Ankwyell/Prusa3/reprap-i3/doc/framestep1.png

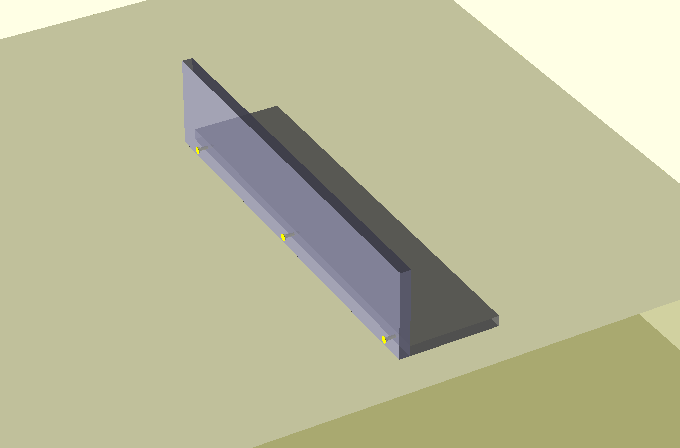
reprap-i3/doc/framestep1.png
