Ankwyell/Prusa3/reprap-i3/doc/framestep3.png

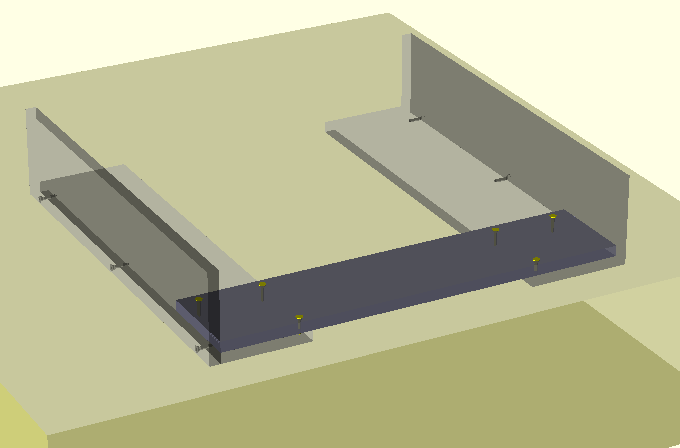
reprap-i3/doc/framestep3.png
