Ankwyell/Prusa3/reprap-i3/doc/framestep5.png

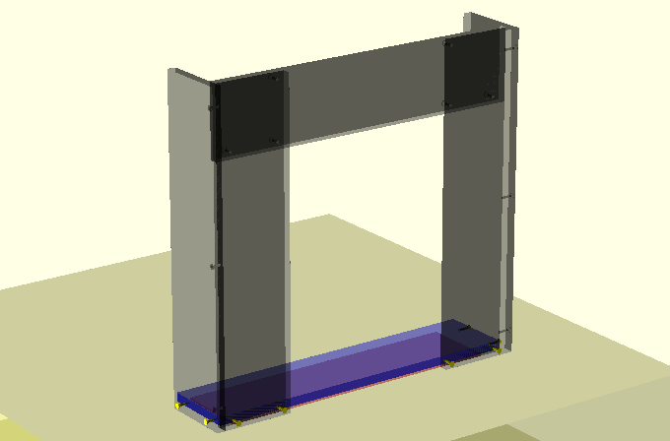
reprap-i3/doc/framestep5.png
