Ankwyell/Prusa3/reprap-i3/doc/ystep1.png

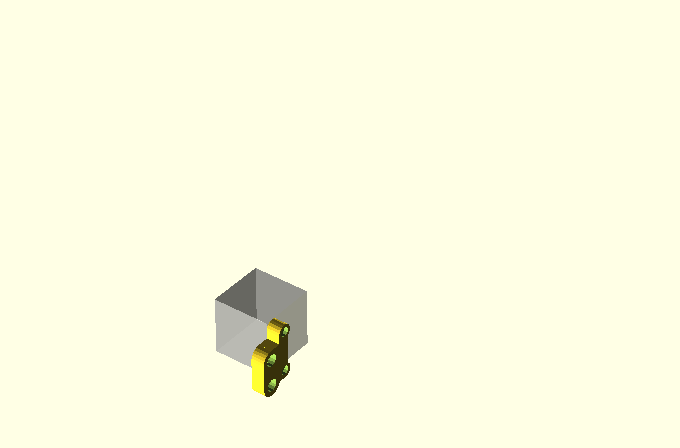
reprap-i3/doc/ystep1.png
