Ankwyell/Prusa3/reprap-i3/doc/ystep3.png

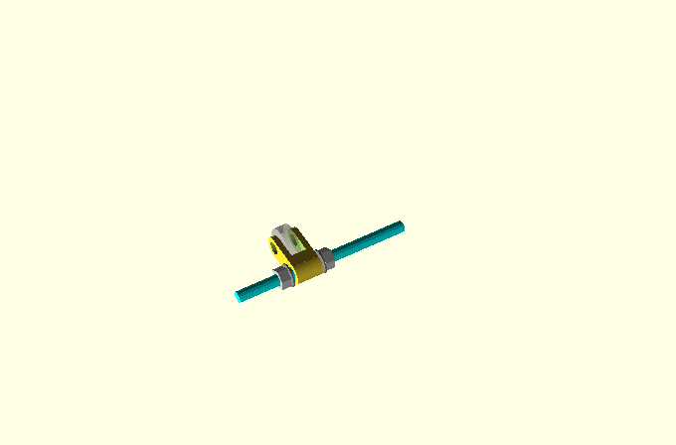
reprap-i3/doc/ystep3.png
