Ankwyell/Prusa3/reprap-i3/doc/ystep6.png

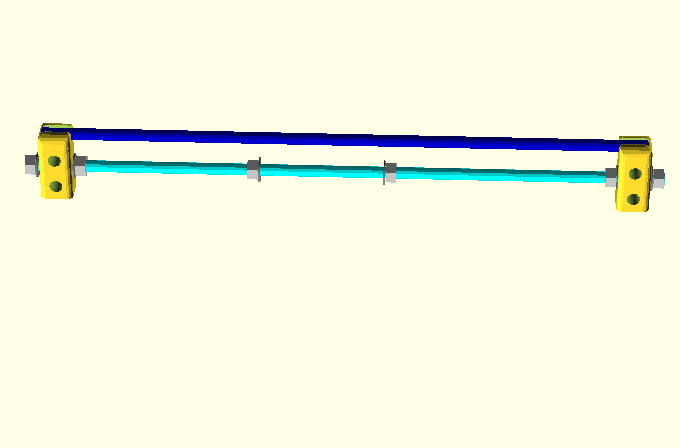
reprap-i3/doc/ystep6.png
