Ankwyell/Prusa3/reprap-i3/doc/ystep7.png

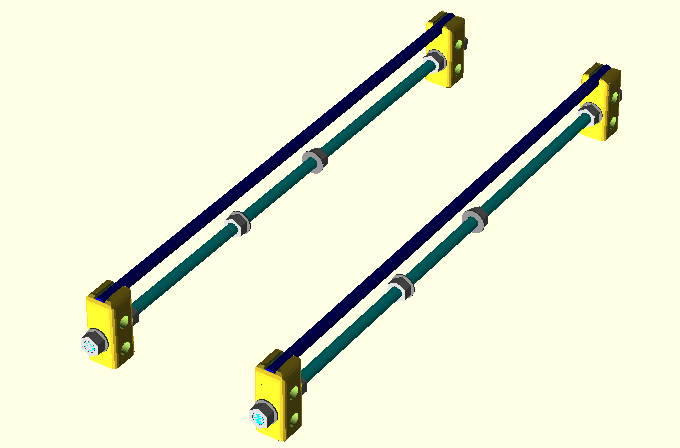
reprap-i3/doc/ystep7.png
