Ankwyell/Prusa3/reprap-i3/doc/ystep8.png

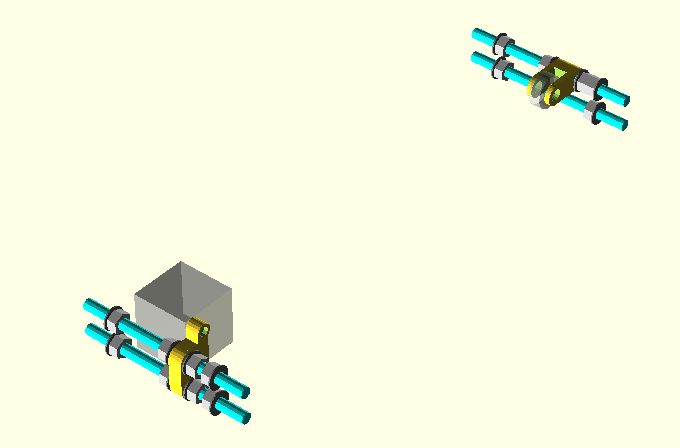
reprap-i3/doc/ystep8.png
