Ankwyell/Prusa3/reprap-i3/doc/ystep9.png

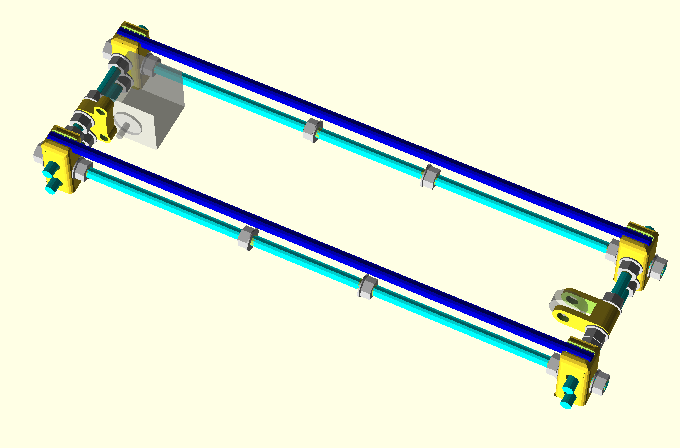
reprap-i3/doc/ystep9.png
