Ankwyell/Prusa3/reprap-i3/doc/ystep10.png

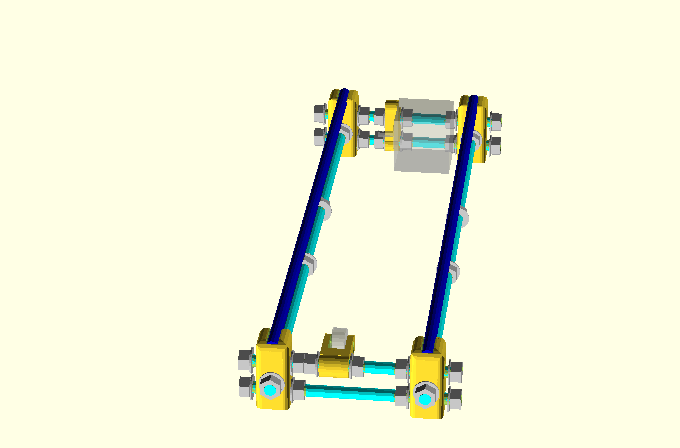
reprap-i3/doc/ystep10.png
