Ankwyell/Prusa3/reprap-i3/doc/ystep11.png

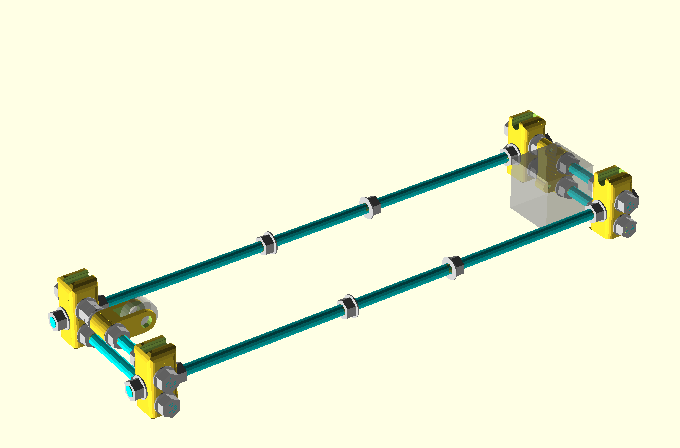
reprap-i3/doc/ystep11.png
