Ankwyell/Prusa3/reprap-i3/sample_stls/single_plate_gt2_lm8uu/extras/calibrate.stl

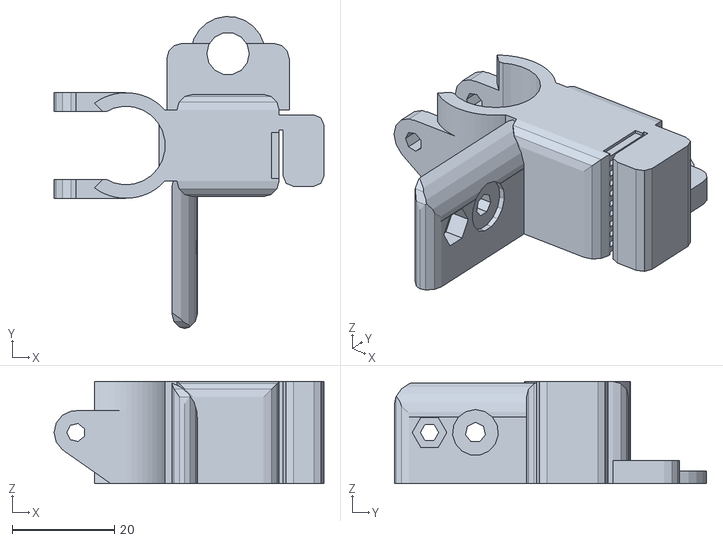
[picture p31: CAD file, 2014-08-09]
reprap-i3/sample_stls/single_plate_gt2_lm8uu/extras/calibrate.stl
52.9 x 61.1 x 20.0
