Ankwyell/Prusa3/reprap-i3/sample_stls/big_htd3_lm12luu/x-carriage.stl

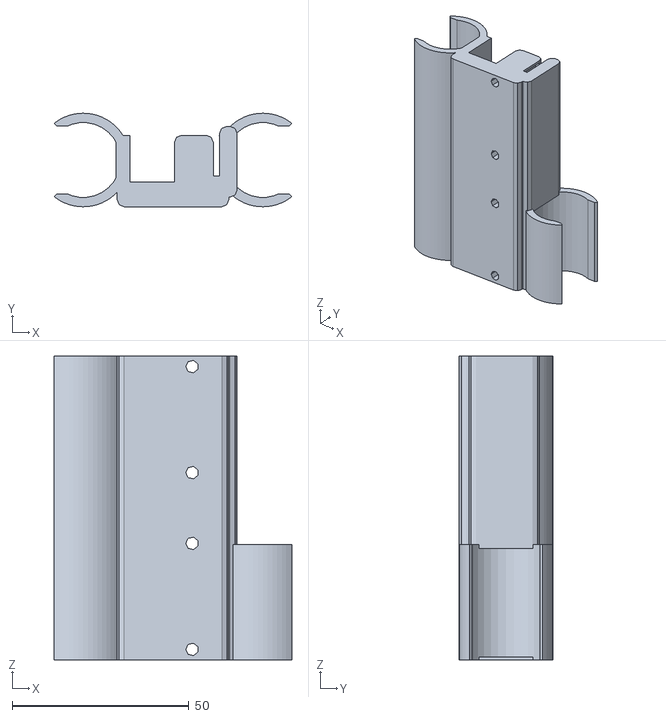
[picture p32: CAD file, 2014-08-09]
reprap-i3/sample_stls/big_htd3_lm12luu/x-carriage.stl
67.2 x 26.5 x 86.0
