Ankwyell/Prusa3/reprap-i3/sample_stls/default_box_gt2_lm10uu/bushing.stl

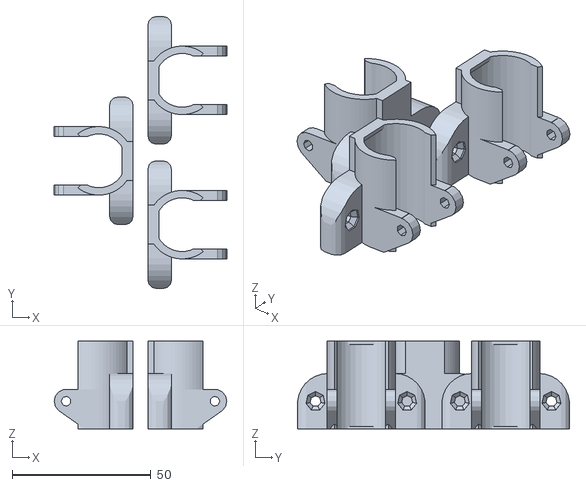
[picture p33: CAD file, 2014-08-09]
reprap-i3/sample_stls/default_box_gt2_lm10uu/bushing.stl
62.2 x 98.0 x 31.7
