Ankwyell/Prusa3/reprap-i3/sample_stls/default_box_gt2_lm10uu/extras/wade-gears.stl

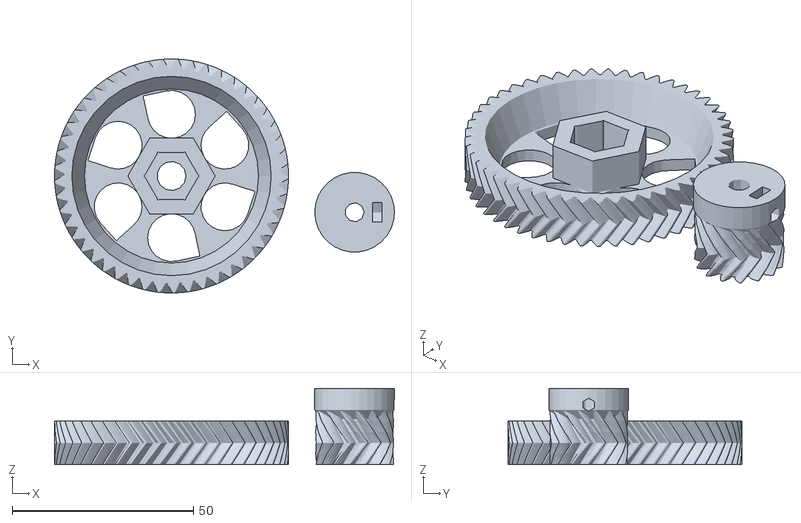
[picture p34: CAD file, 2014-08-09]
reprap-i3/sample_stls/default_box_gt2_lm10uu/extras/wade-gears.stl
93.8 x 64.5 x 21.0
