Ankwyell/Prusa3/reprap-i3/sample_stls/single_plate_gt2_lm8uu/y-axis-corner.stl

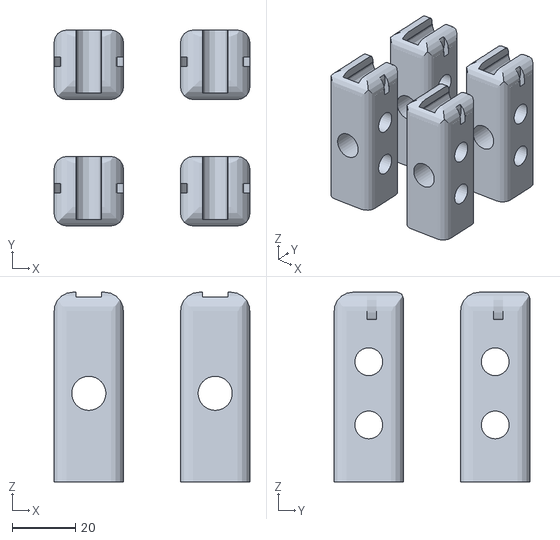
[picture p35: CAD file, 2014-08-09]
reprap-i3/sample_stls/single_plate_gt2_lm8uu/y-axis-corner.stl
62.0 x 62.0 x 60.0
