Ankwyell/Prusa3/reprap-i3/sample_stls/big_htd3_lm12luu/y-drivetrain.stl

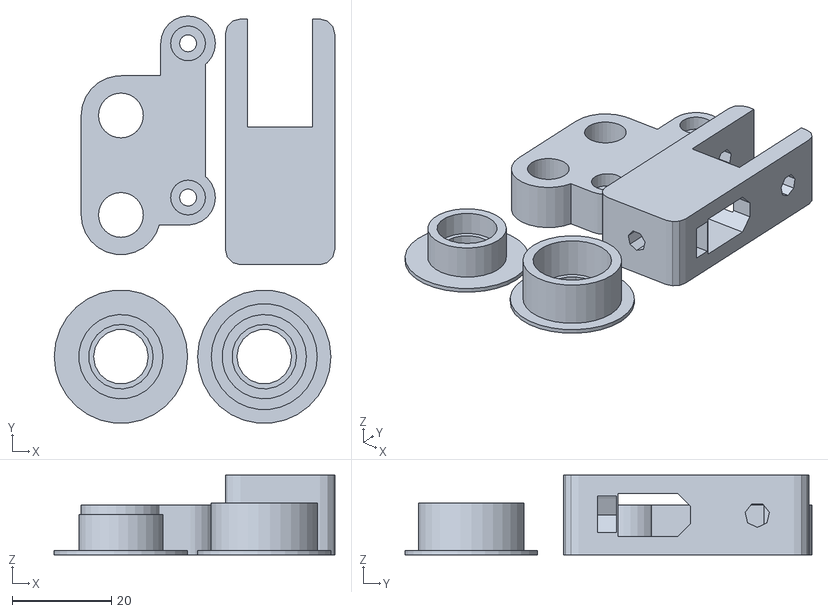
[picture p36: CAD file, 2014-08-09]
reprap-i3/sample_stls/big_htd3_lm12luu/y-drivetrain.stl
56.4 x 81.8 x 16.0
