Ankwyell/Prusa3/reprap-i3/sample_stls/default_box_gt2_lm10uu/y-axis-bracket.stl

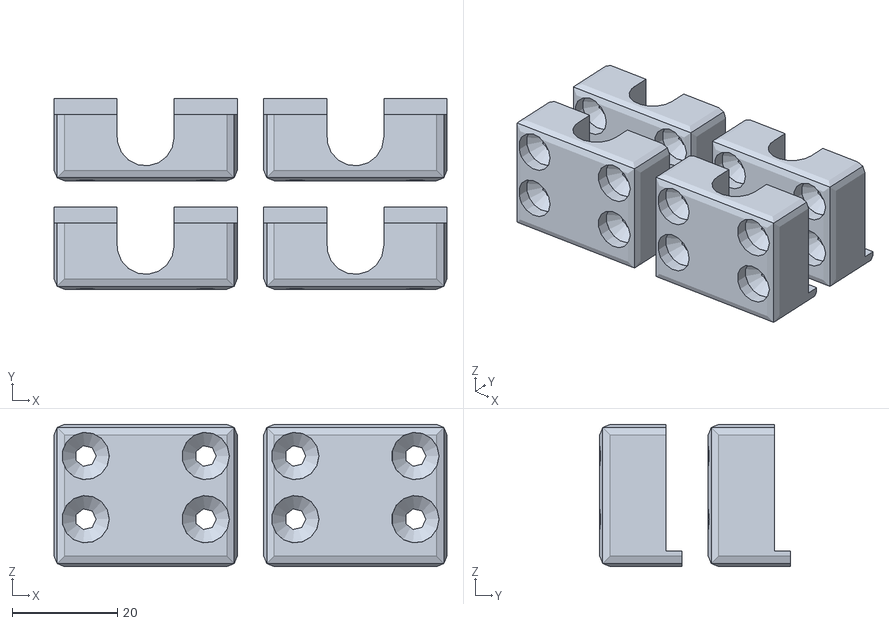
[picture p37: CAD file, 2014-08-09]
reprap-i3/sample_stls/default_box_gt2_lm10uu/y-axis-bracket.stl
74.6 x 36.2 x 27.0
