Ankwyell/Prusa3/reprap-i3/sample_stls/single_plate_gt2_lm8uu/extras/bearing-holder-single-plate-y.stl

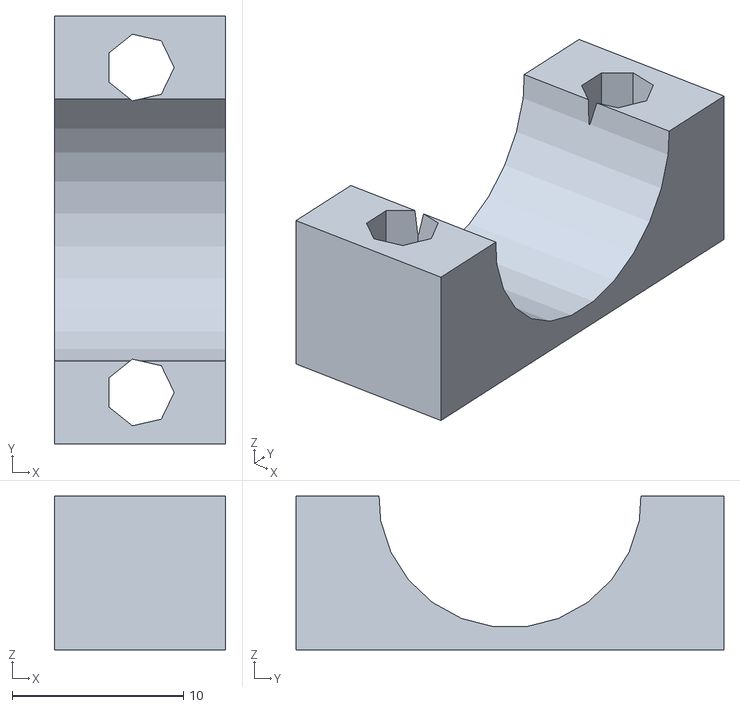
[picture p38: CAD file, 2014-08-09]
reprap-i3/sample_stls/single_plate_gt2_lm8uu/extras/bearing-holder-single-plate-y.stl
10.0 x 25.0 x 9.00
