Ankwyell/Prusa3/reprap-i3/sample_stls/single_plate_gt2_lm8uu/x-end.stl

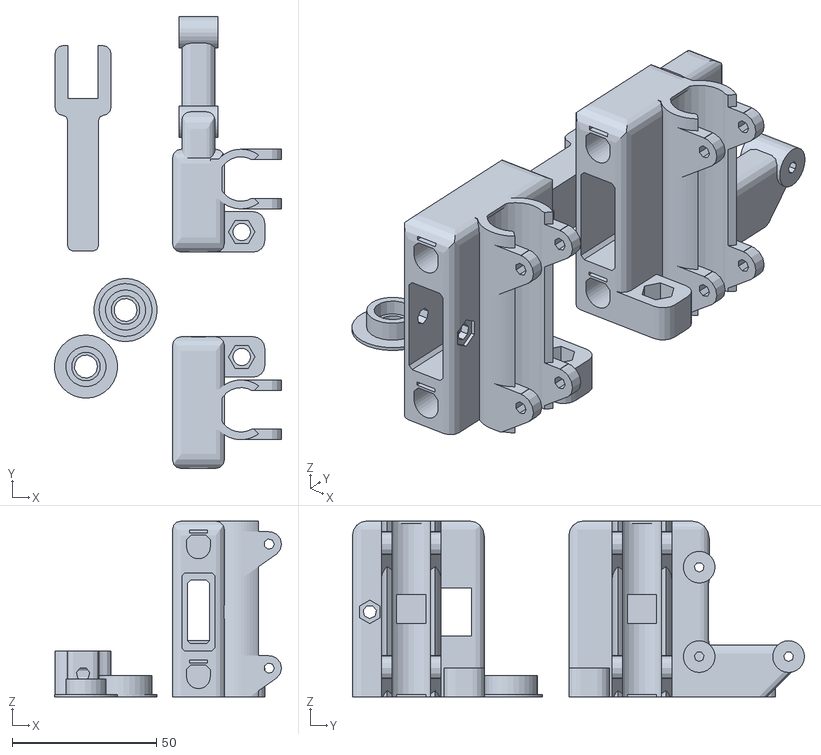
[picture p39: CAD file, 2014-08-09]
reprap-i3/sample_stls/single_plate_gt2_lm8uu/x-end.stl
78.7 x 156.7 x 61.0
