Ankwyell/Prusa3/reprap-i3/sample_stls/big_htd3_lm12luu/bushing.stl

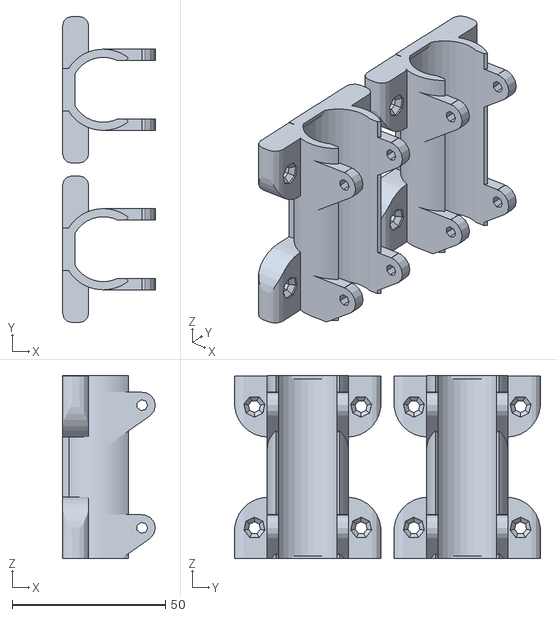
[picture p40: CAD file, 2014-08-09]
reprap-i3/sample_stls/big_htd3_lm12luu/bushing.stl
30.2 x 99.8 x 59.7
