Ankwyell/Prusa3/reprap-i3/sample_stls/single_plate_gt2_lm8uu/z-axis.stl

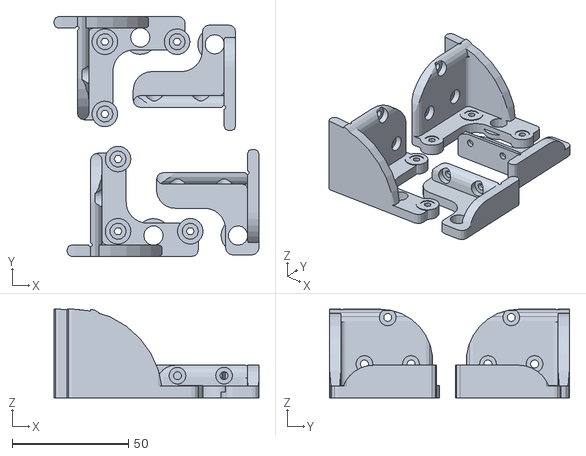
[picture p41: CAD file, 2014-08-07]
reprap-i3/sample_stls/single_plate_gt2_lm8uu/z-axis.stl
88.0 x 103.0 x 38.0
