Ankwyell/Prusa3/reprap-i3/sample_stls/default_box_gt2_lm10uu/y-belt-holder.stl

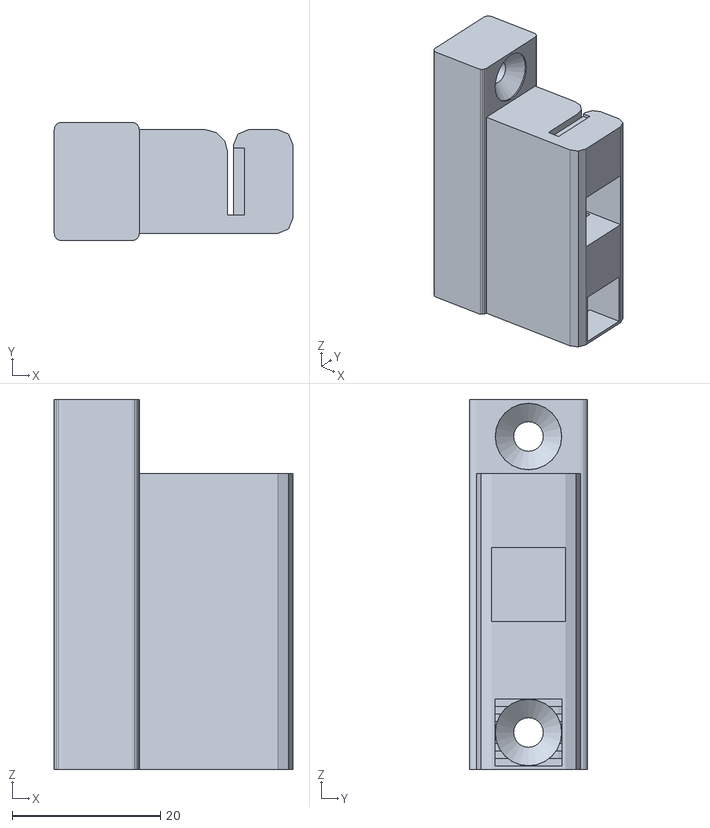
[picture p42: CAD file, 2014-08-09]
reprap-i3/sample_stls/default_box_gt2_lm10uu/y-belt-holder.stl
32.2 x 16.0 x 50.0
