Ankwyell/Prusa3/reprap-i3/sample_stls/big_htd3_lm12luu/z-axis.stl

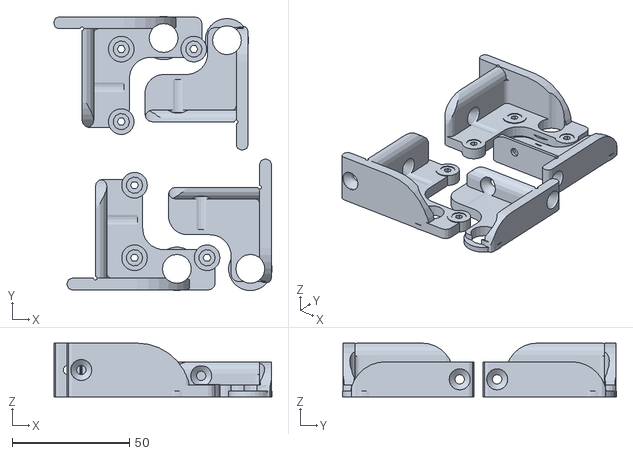
[picture p43: CAD file, 2014-08-07]
reprap-i3/sample_stls/big_htd3_lm12luu/z-axis.stl
93.1 x 117.2 x 23.0
