Ankwyell/Prusa3/reprap-i3/sample_stls/default_box_gt2_lm10uu/z-axis.stl

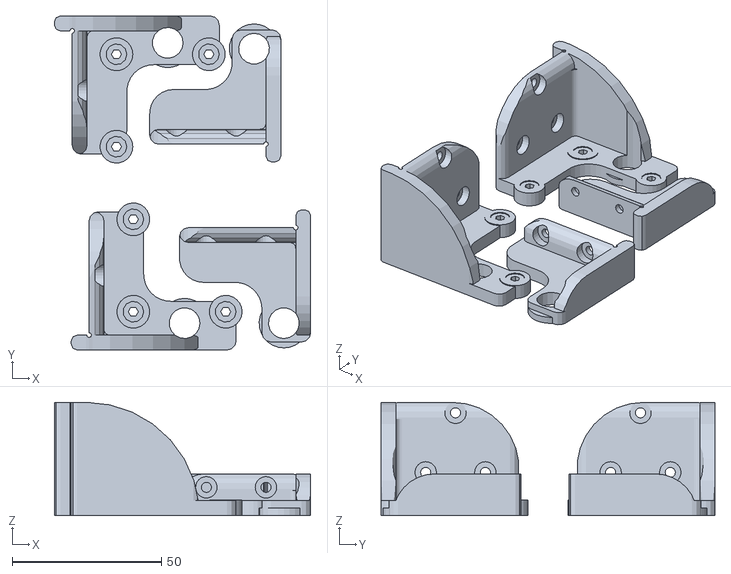
[picture p44: CAD file, 2014-08-07]
reprap-i3/sample_stls/default_box_gt2_lm10uu/z-axis.stl
86.0 x 112.0 x 38.0
